tetrodekazz/TACOpi_3_GTR/camera_botrtom_screw.jpg

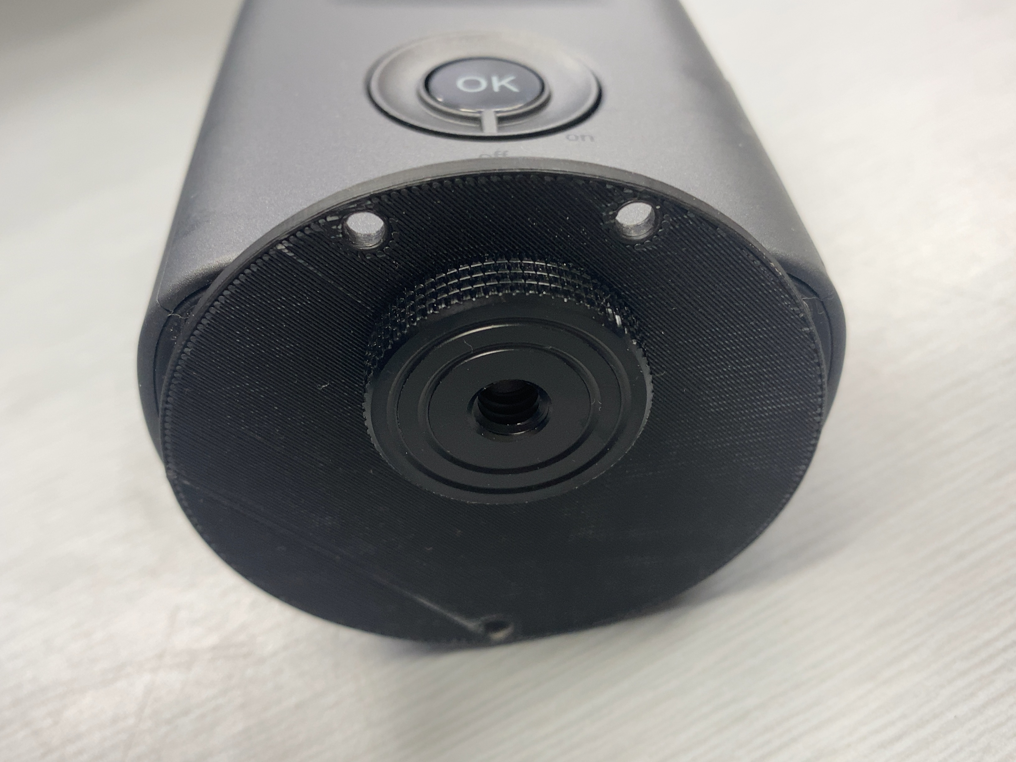
camera_botrtom_screw.jpg
