tetrodekazz/TACOpi_3_GTR/deployment.jpg

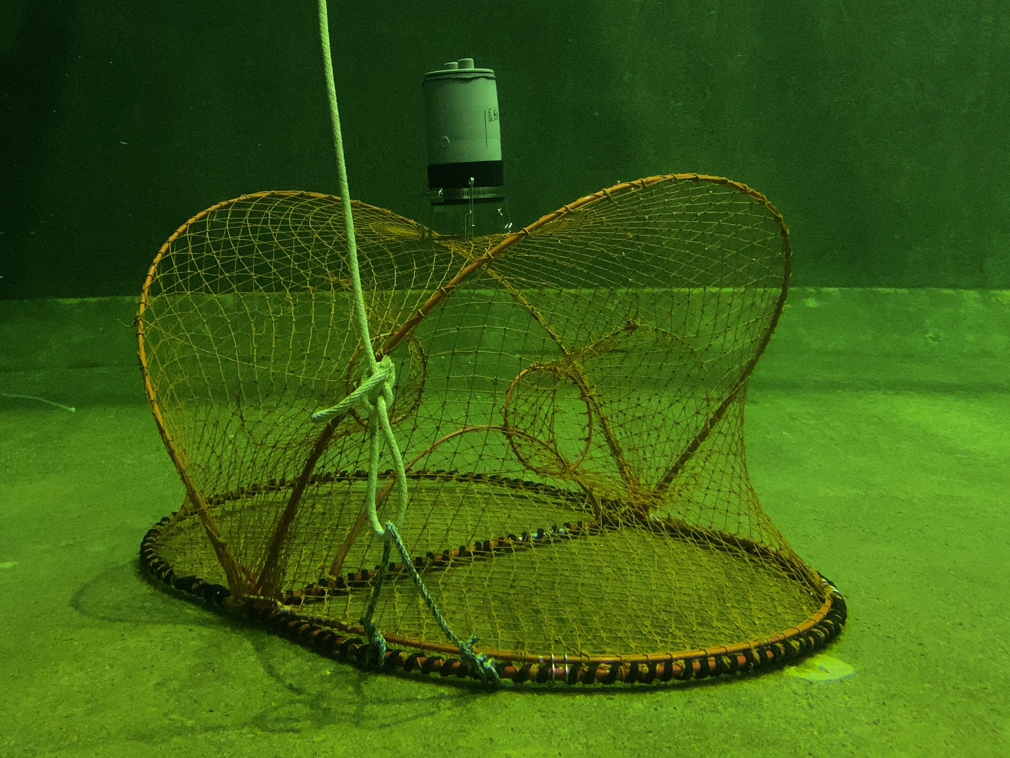
deployment.jpg
