tetrodekazz/TACOpi_3_GTR/examplephoto.jpg

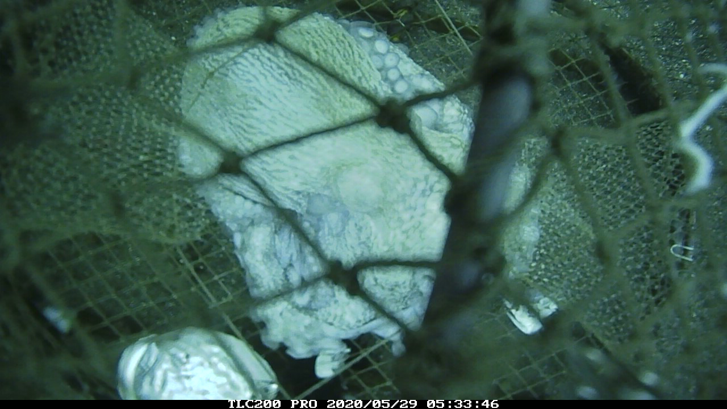
examplephoto.jpg
