tetrodekazz/TACOpi_3_GTR/temp_logger.jpg

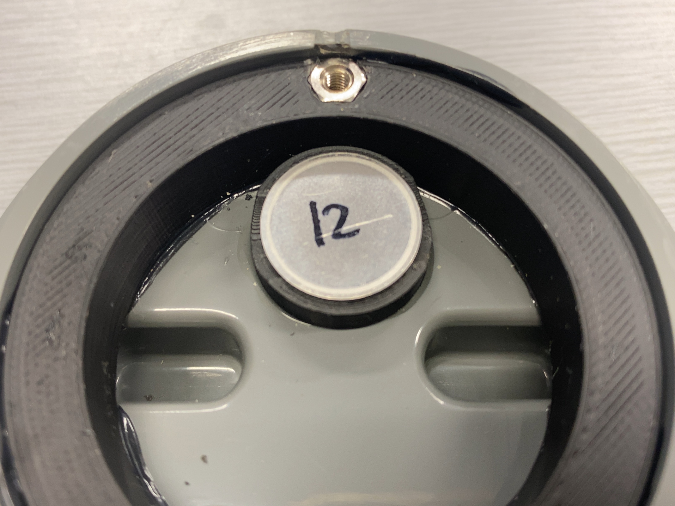
temp_logger.jpg
